filipdumitrascu/ebook_reader/Images/battery.png

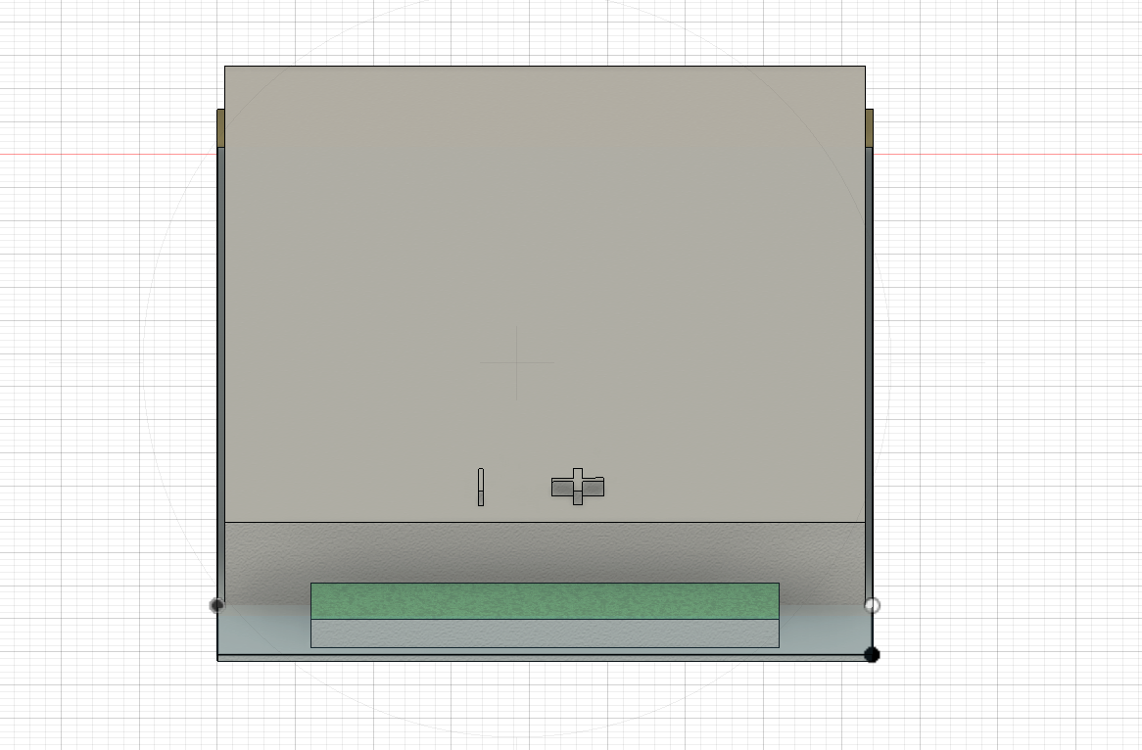
Images/battery.png
