filipdumitrascu/ebook_reader/Images/display side.png

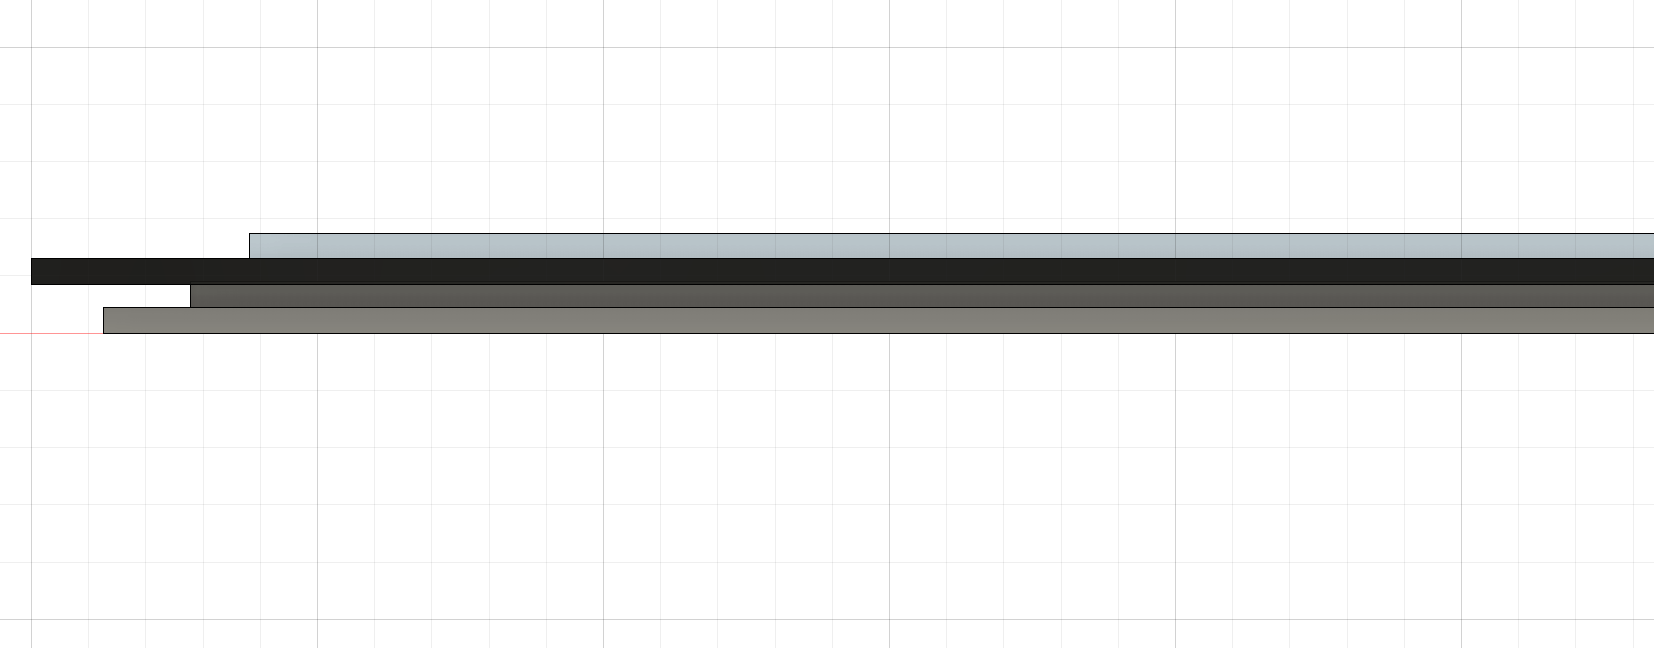
Images/display side.png
