filipdumitrascu/ebook_reader/Images/openbook enclosure back.png

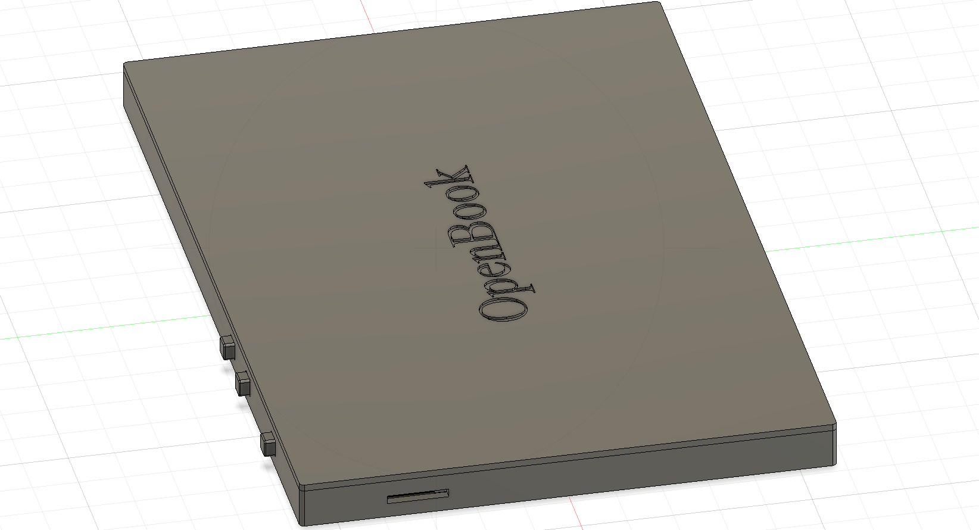
Images/openbook enclosure back.png
