filipdumitrascu/ebook_reader/Images/openbook enclosure bottom.png

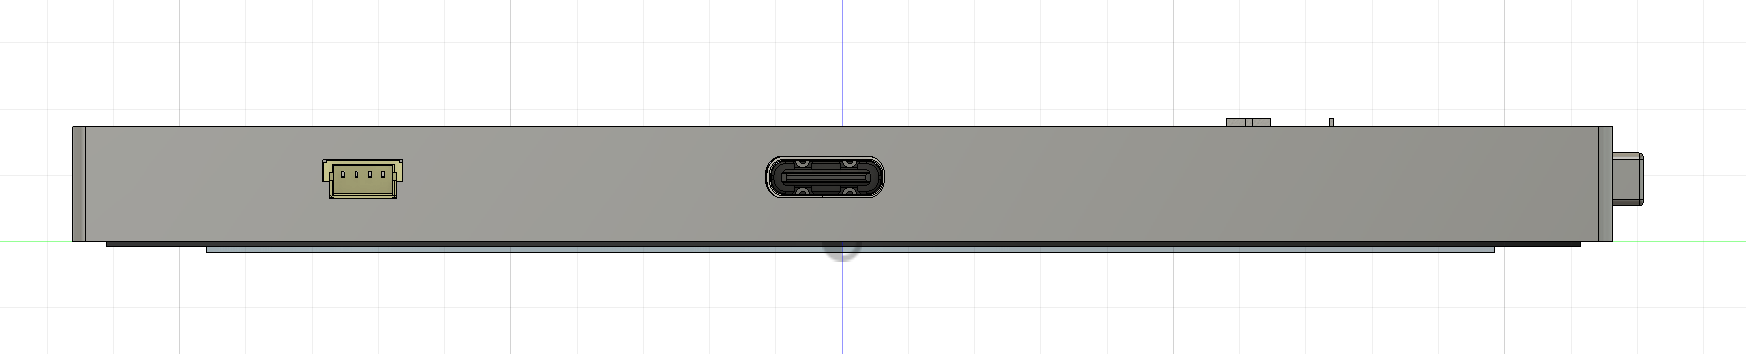
Images/openbook enclosure bottom.png
