filipdumitrascu/ebook_reader/Images/pcb back.png

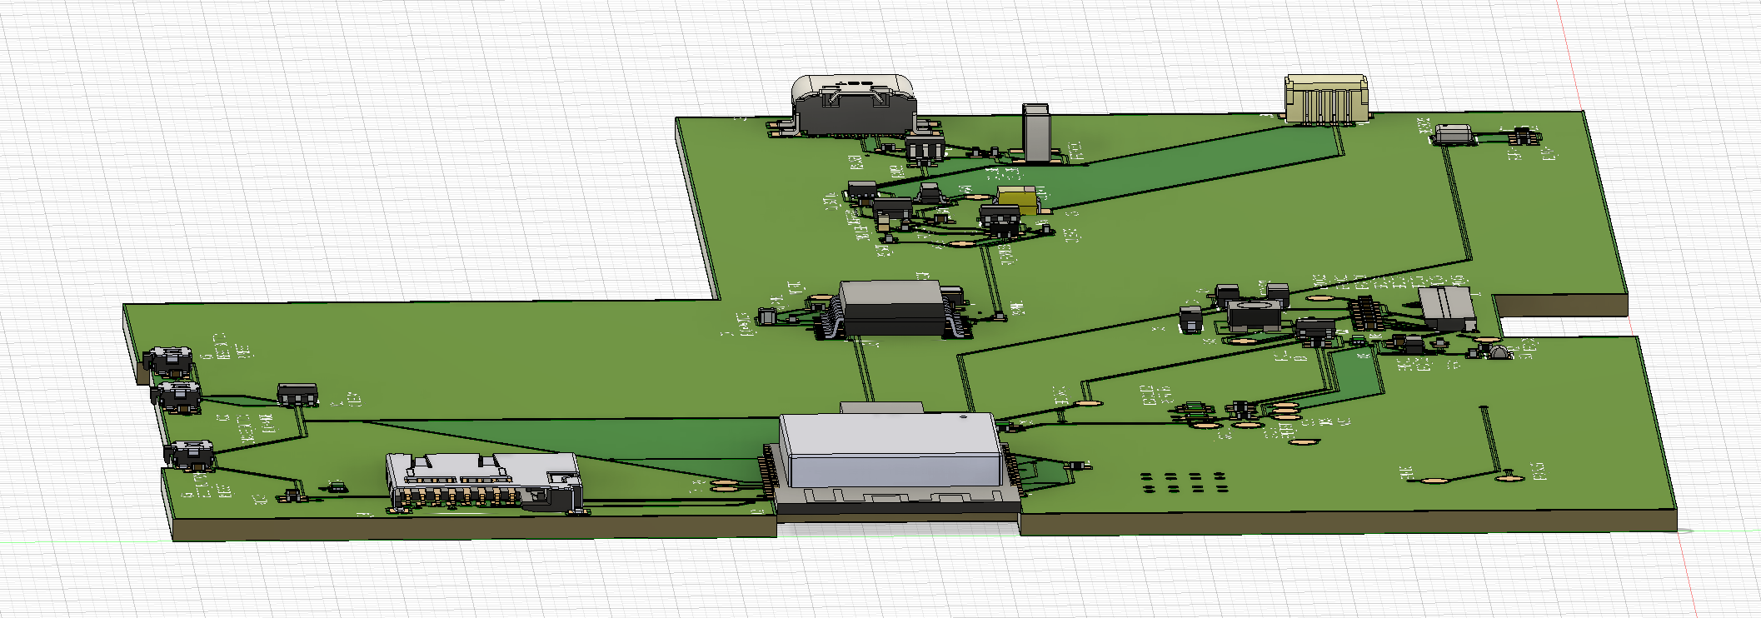
Images/pcb back.png
