filipdumitrascu/ebook_reader/Images/pcb left.png

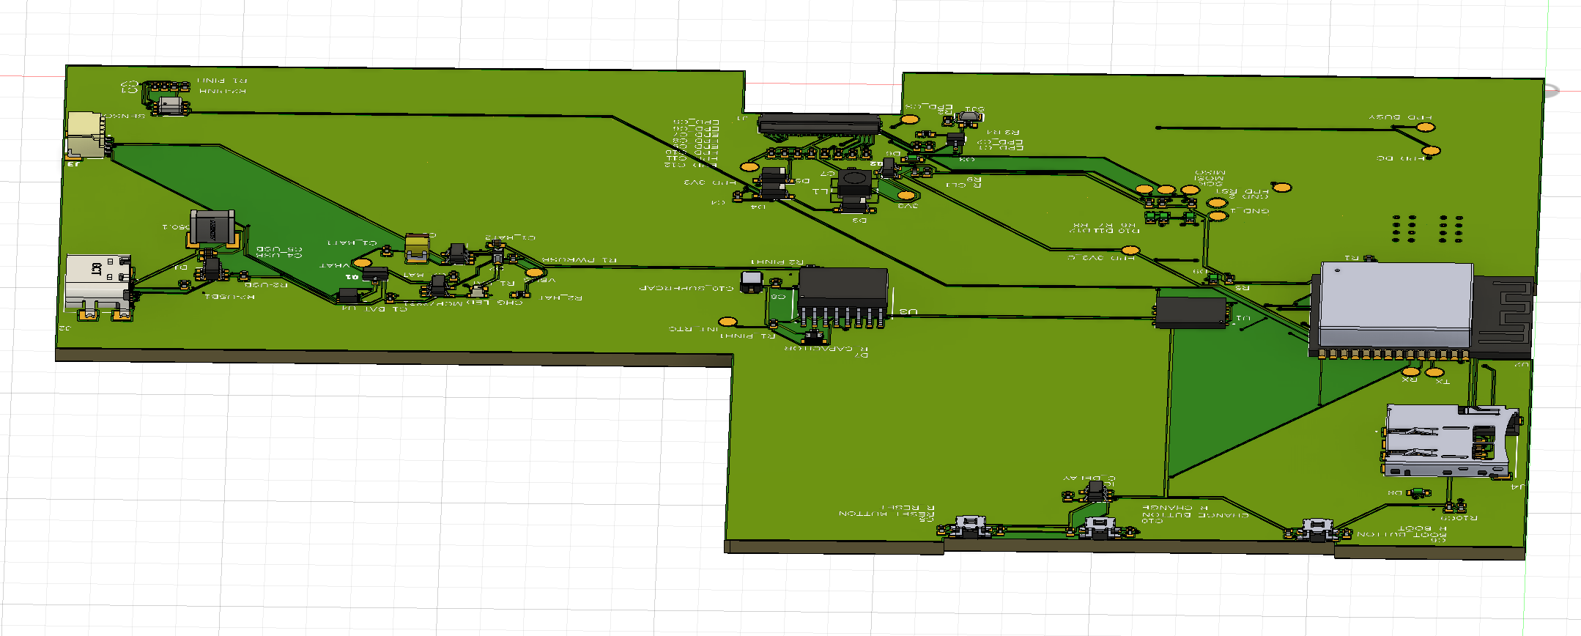
Images/pcb left.png
