filipdumitrascu/ebook_reader/Images/pcb right.png

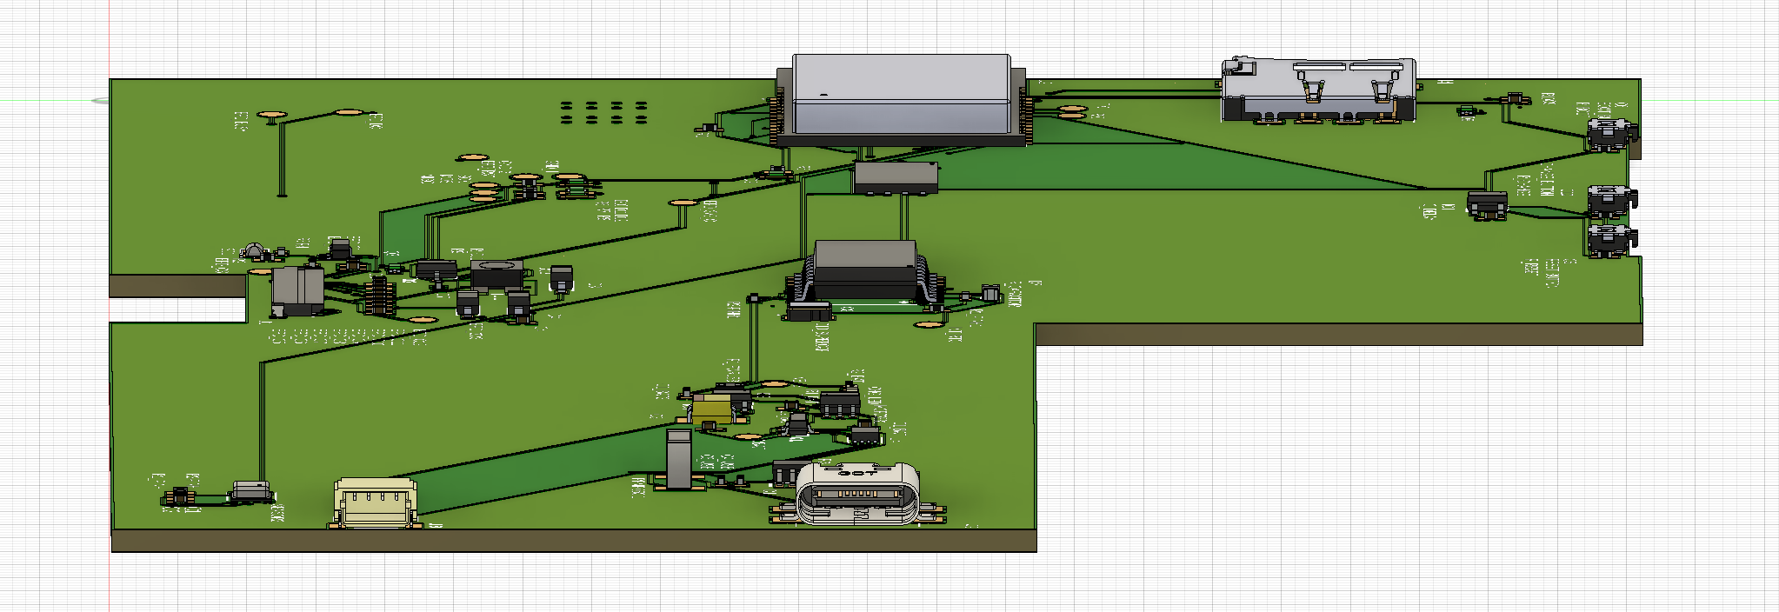
Images/pcb right.png
